makerust/TheKNOB/Hardware/CaseAndMechanism/SolidworksFiles/NeoPixelPCBA.SLDPRT

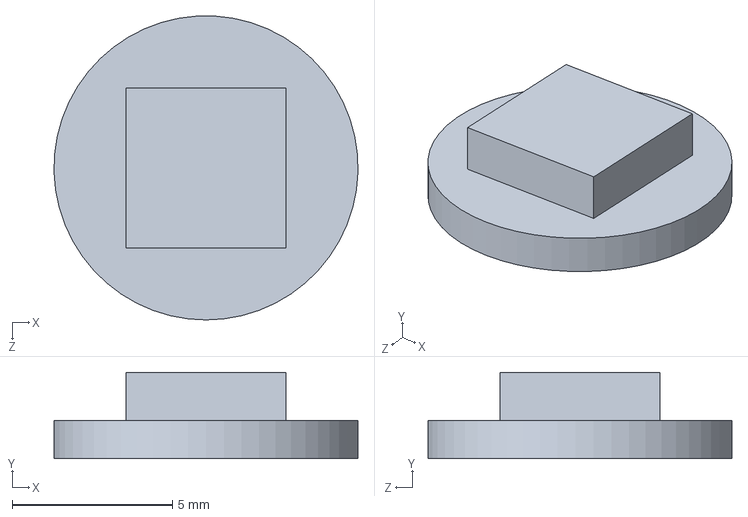
[picture p15: CAD file, 2021-12-21]
Hardware/CaseAndMechanism/SolidworksFiles/NeoPixelPCBA.SLDPRT
9.50 x 2.70 x 9.49 mm
