makerust/TheKNOB/Hardware/CaseAndMechanism/SolidworksFiles/9714K428_Wave Disc Spring.SLDPRT

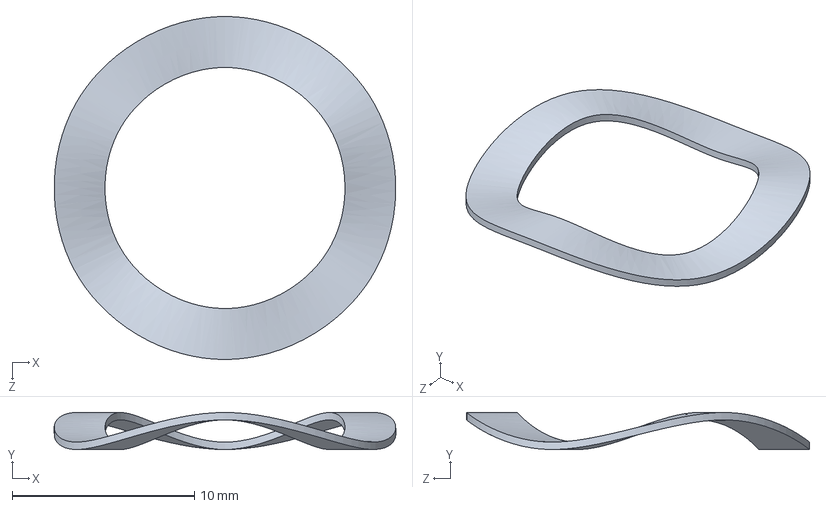
[picture p16: CAD file, 2021-12-21]
Hardware/CaseAndMechanism/SolidworksFiles/9714K428_Wave Disc Spring.SLDPRT
18.7 x 2.03 x 18.8 mm
