makerust/TheKNOB/Hardware/CaseAndMechanism/SolidworksFiles/98689A118_General Purpose 18-8 Stainless Steel Washer.SLDPRT

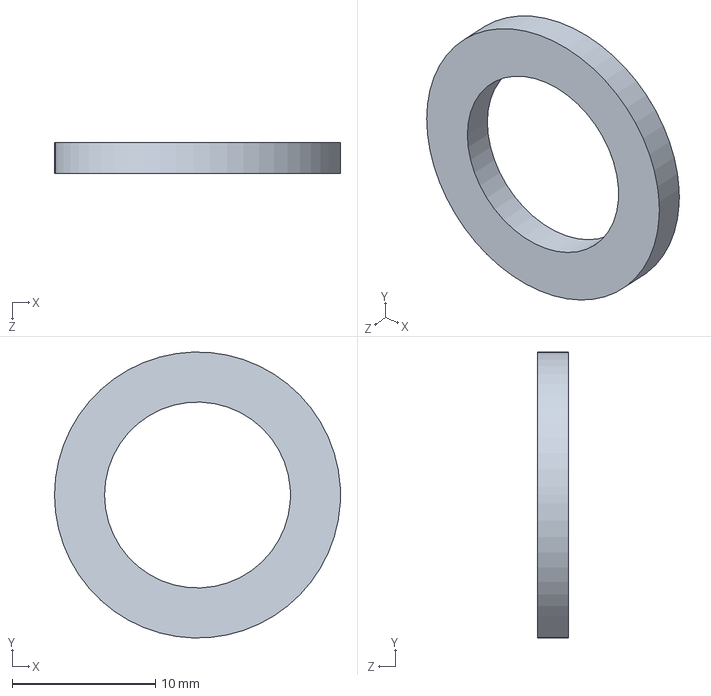
[picture p17: CAD file, 2021-12-21]
Hardware/CaseAndMechanism/SolidworksFiles/98689A118_General Purpose 18-8 Stainless Steel Washer.SLDPRT
20.0 x 20.0 x 2.20 mm
